CrypticPoet/off-grid-energy-design/Review_Tribe_B.md

# Feedback Tribe A
##### Q1. Did this tribe get evaluated correctly ? Qualify your Yes/No with reasons.
This tribe should be given 10 marks out of 15. Majorly other marks are cut because of the extensively poor readablity and data overflow of the report. Otherwise other aspects are fine. 

##### Q2. What are the best things (point wise) you observed in this Tribe's report ? These are points you will incorporate in your next Report.
- Great explaining each readablity index.
- Good job incorporating the Critical path for the project.
- Giffy explaination is good since it gives you a simple model of the system.
- Great design section, includes all major FOV and model renders are very good as well. Plan for the house is also very appropriately done.
- Great Job in Appendix section.

##### Q3. What are the worst things (point wise) you observed in this Tribe's report ? These are points you will avoid in your next report.
- Table of contents not made very properly.
- Gantt Chart could have been improved.
- Data in the requirements needs to be more generalised by using tables instead of paragraphs which are harder to read and understand.
- Links could have been added properly in the pdf file where mentioning the whole URL can be avoided.
- Specifications for no reason include so much explainations about the working and composition for each material. These could have been easily avoided and a seperate section to explain the process and calculations from there can be incorporated in specifications.
- Cannot comprehend what was the need to mention the whole warranty specification for each product here even when most products of similar specifications will have similar warranty and a link to the warranty could have been included saving extra reading time for the reader.
- Bill of materials not done in a proper way i.e. similar to bill reciepts.

##### Q4. Please make some good appreciative / encouraging / positive comments about the effort made by this Tribe in putting together their report. Organize your comments on the rubric of sub-efforts – documentation, technical content, team work, tool usage, readability, usability for a possible product offering.
The overall project report was very inclusive of every possible aspect. Documentation, Technical content, Team work, Tool usage were upto the mark but readablity and usability of this report might need some work which can be definitely incorporated in next project cycle. Overall the efforts put in the project were outstanding.
