CrypticPoet/off-grid-energy-design/Project Management/proj-manage.md

<p align="center">
	 Gantt chart 
	 <figcaption align="center">Gantt Chart</figcaption>
</p>

The red path in the above Gantt Chart shows the critical path. It was closely monitored, so that there were no delays in the corresponding works.

The following shows the start dates and durations of various subteams in the project:

<p align="center">
	  
	 <figcaption align="center">Sunergy</figcaption>
</p>

The following shows the resources available, a gear symbol against a name shows that they were involved in the project
<p align="center">
	 Resource management 
	 <figcaption align="center">Resources</figcaption>
</p>

The following shows the work breakdown structure:
<p align="center">
	 Work Breakdown Structure 
	 <figcaption align="center">Assignment of Work</figcaption>
</p>
<p align="center">
	 Work Breakdown Structure 
	 <figcaption align="center">Project Management</figcaption>
</p>
<p align="center">
	 Work Breakdown Structure 
	 <figcaption align="center">CAD Model</figcaption>
</p>
<p align="center">
	 Work Breakdown Structure 
	 <figcaption align="center">LT Spice Circuit design</figcaption>
</p>
<p align="center">
	 Work Breakdown Structure 
	 <figcaption align="center">Specifications</figcaption>
</p>
<p align="center">
	 Work Breakdown Structure 
	 <figcaption align="center">Documentation</figcaption>
</p>
