CrypticPoet/off-grid-energy-design/Project Management/gantt1.png

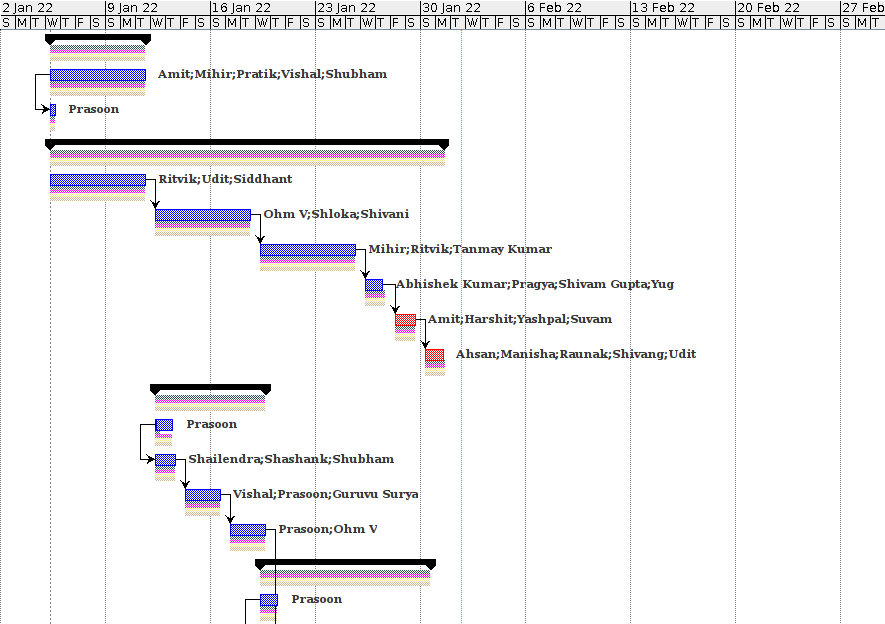
Project Management/gantt1.png
