CrypticPoet/off-grid-energy-design/Project Management/gantt2.png

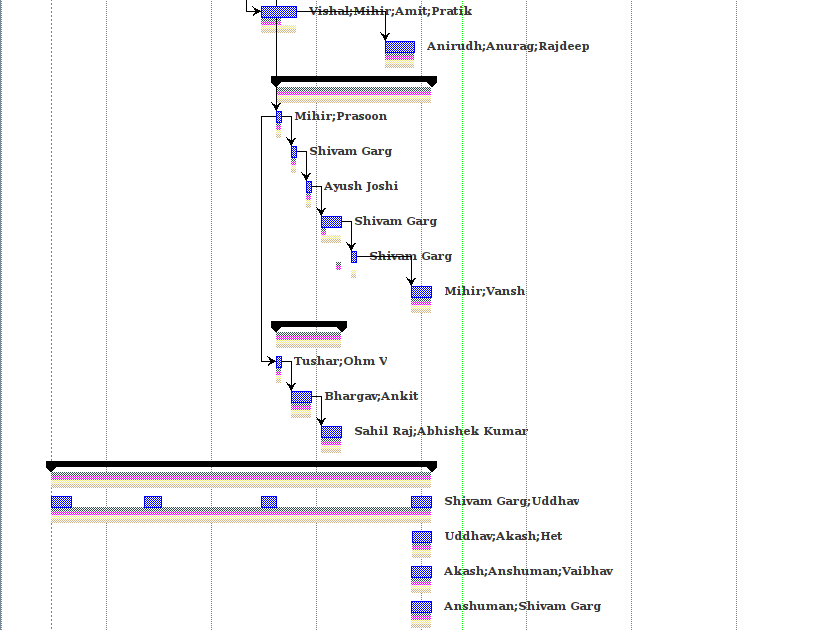
Project Management/gantt2.png
