CrypticPoet/off-grid-energy-design/Project Management/resources1.png

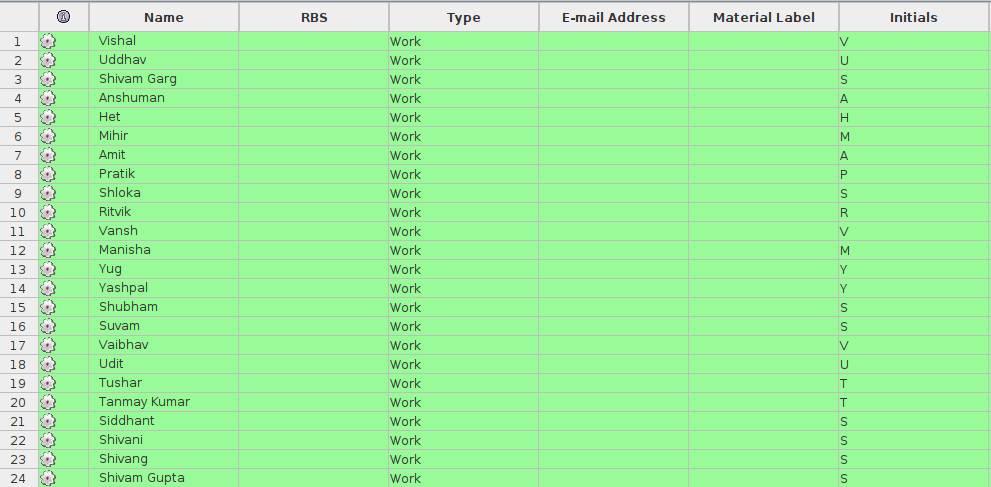
Project Management/resources1.png
