CrypticPoet/off-grid-energy-design/Project Management/resources2.png

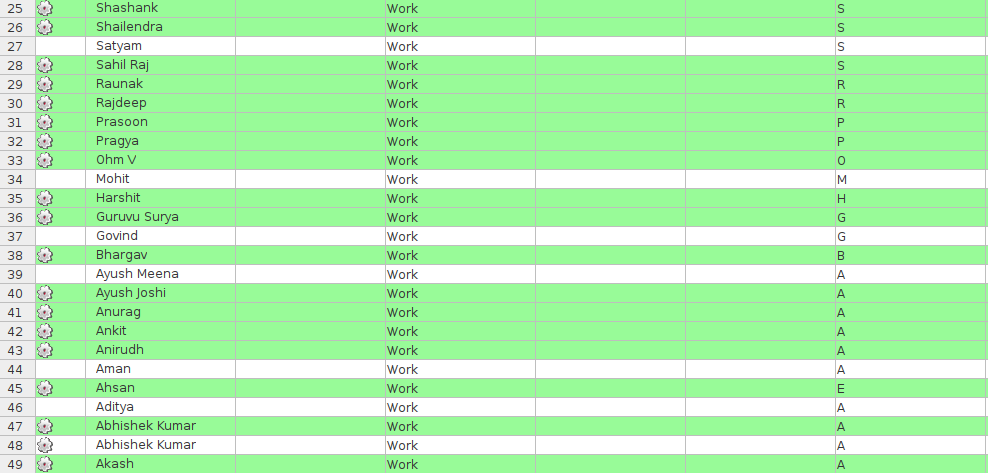
Project Management/resources2.png
