CrypticPoet/off-grid-energy-design/Project Management/sunergy1.png

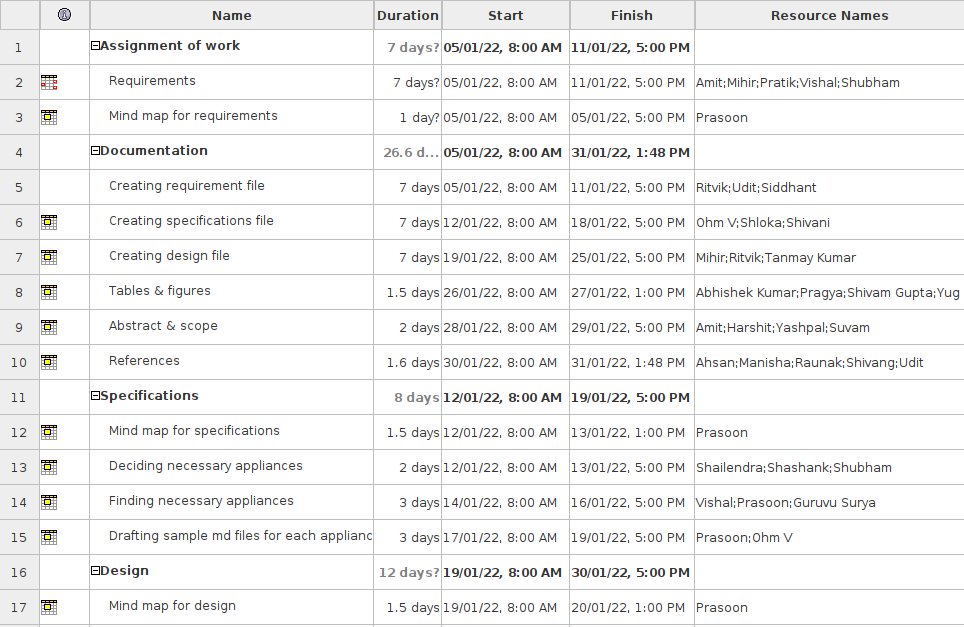
Project Management/sunergy1.png
