CrypticPoet/off-grid-energy-design/Project Management/sunergy2.png

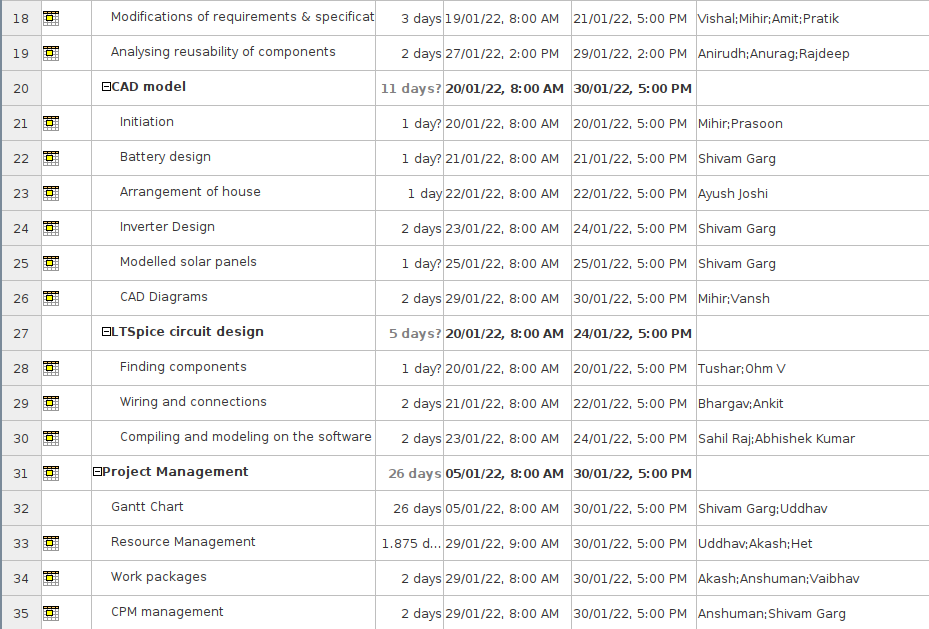
Project Management/sunergy2.png
